uva-linklab/LPCSB/software/apps/squall_beacon/main.c

/*
 * Send an advertisement periodically
 */

#include <stdbool.h>
#include <stdint.h>
#include "nrf_gpio.h"
#include "ble_advdata.h"
// #include "boards.h"
#include "nordic_common.h"
#include "softdevice_handler.h"
#include "ble_debug_assert_handler.h"
#include "led.h"

#include "simple_ble.h"
#include "simple_adv.h"

// Intervals for advertising and connections
static simple_ble_config_t ble_config = {
    .platform_id       = 0x40,              // used as 4th octect in device BLE address
    .device_id         = DEVICE_ID_DEFAULT,
    .adv_name          = "LPCSB_test",       // used in advertisements if there is room
    .adv_interval      = MSEC_TO_UNITS(500, UNIT_0_625_MS),
    .min_conn_interval = MSEC_TO_UNITS(500, UNIT_1_25_MS),
    .max_conn_interval = MSEC_TO_UNITS(1000, UNIT_1_25_MS)
};


int main(void) {
    uint32_t err_code;

    led_init(17);

    // Setup BLE
    simple_ble_init(&ble_config);

    // Advertise because why not
    simple_adv_only_name();

    led_on(17);
    while (1) {
        power_manage();
    }
}
